Natchpai/Electronic_Load/Electronic_load_esp32/Controller.kicad_sch

## KiCad design Electronic_load_esp32/Controller.kicad_sch (2025-04-01)

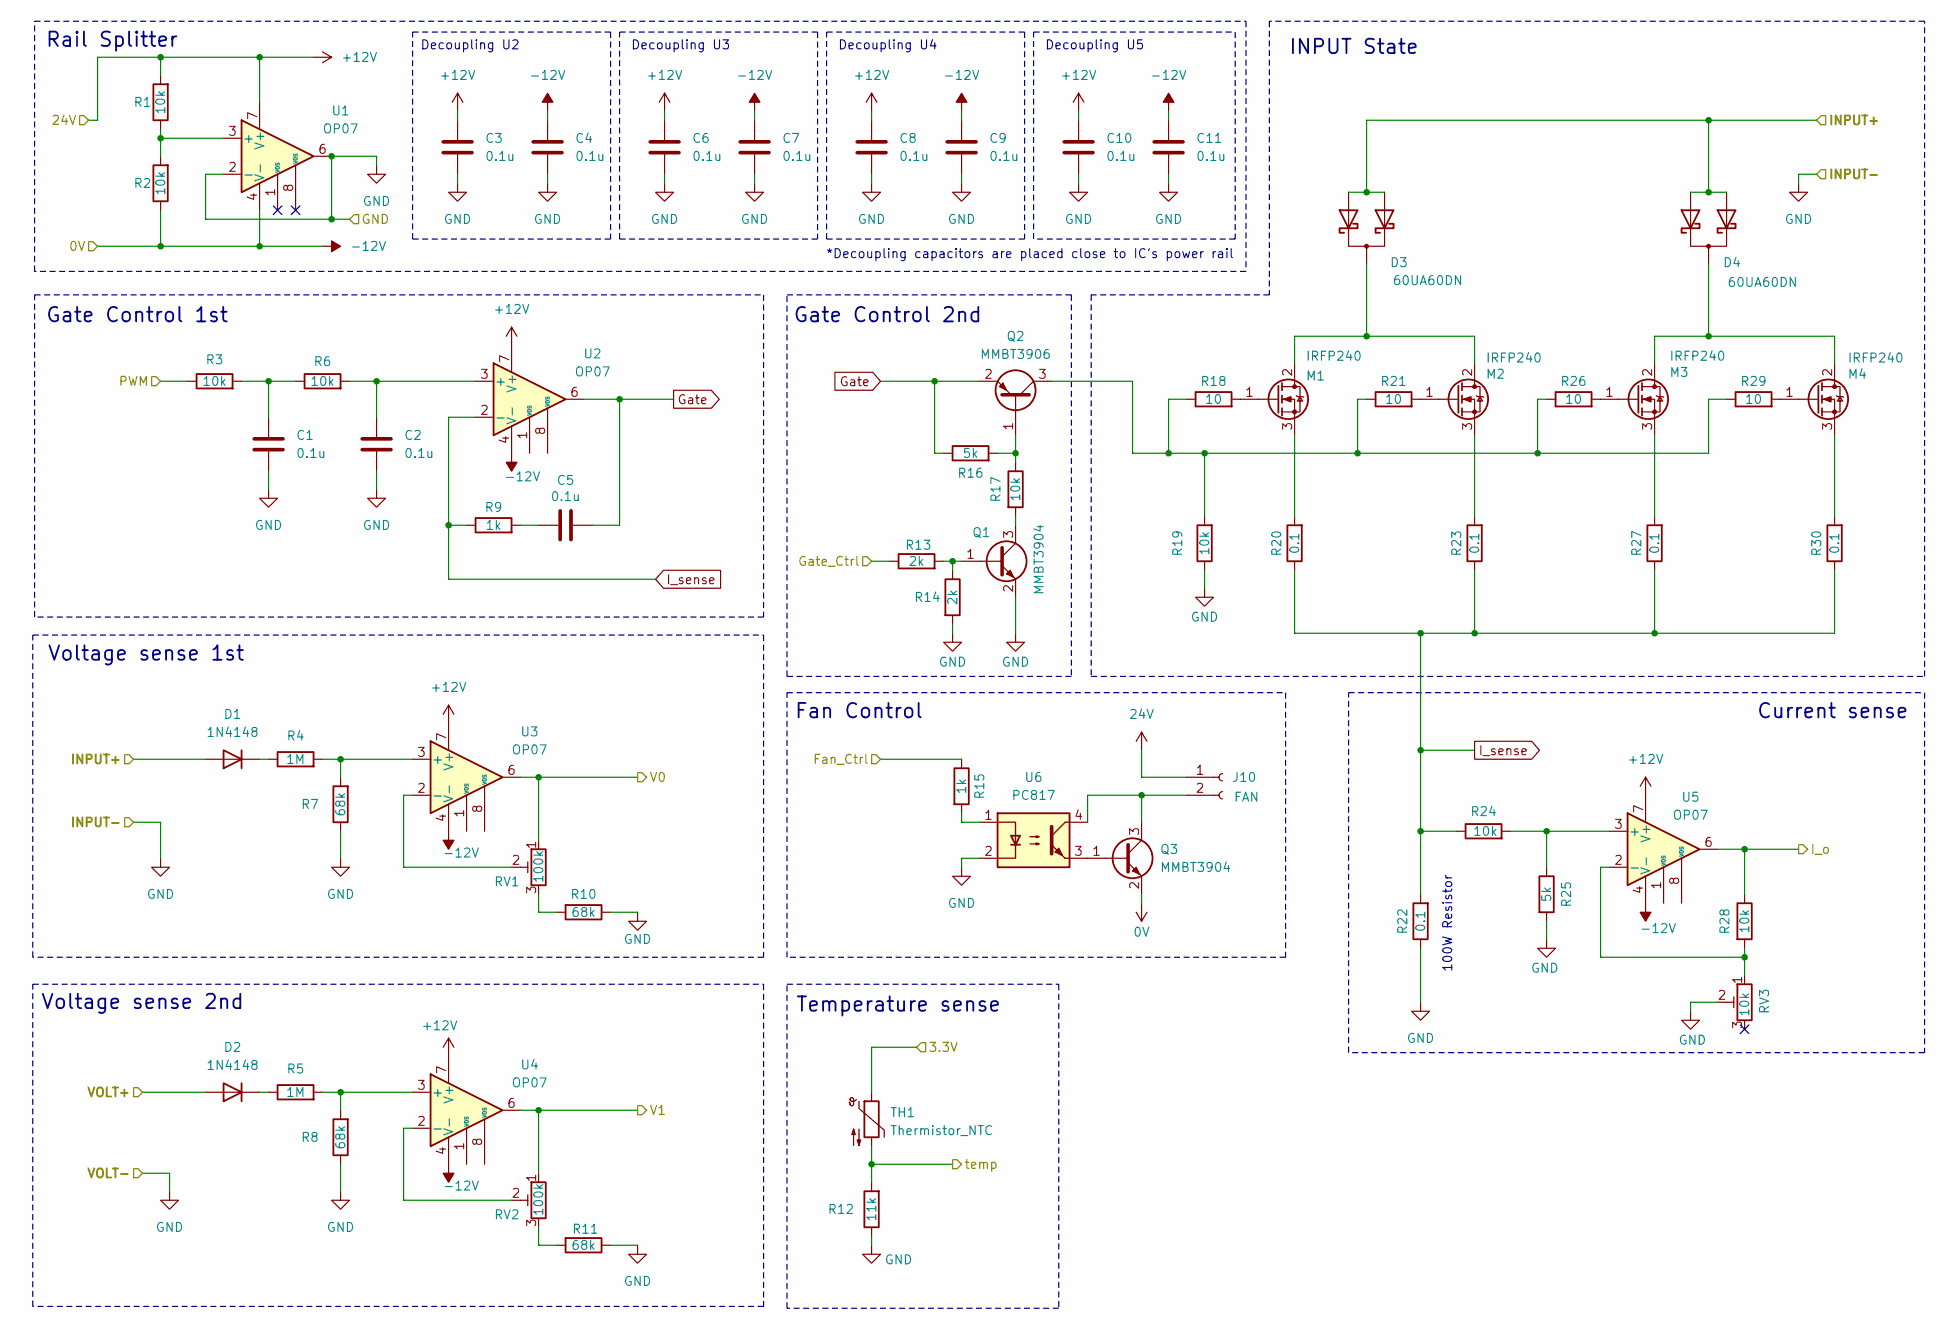
[picture p27: schematic Controller.kicad_sch]

Parts:
C1, C2, C3, C4, C5, C6, C7, C8, C9, C10, C11: 0.1u; C_0603_1608Metric
D1, D2: 1N4148; D_DO-35_SOD27_P7.62mm_Horizontal
D3, D4: 60UA60DN; D_P600_R-6_P12.70mm_Horizontal
J10: FAN; JST_XA_B02B-XASK-1_1x02_P2.50mm_Vertical
M1, M2, M3, M4: IRFP240; TO-247-3_Vertical
Q1, Q3: MMBT3904; SOT-23
Q2: MMBT3906; SOT-23
R1, R2, R3, R6, R17, R19, R24, R28: 10k; R_0603_1608Metric
R4, R5: 1M; R_0603_1608Metric
R7, R8, R10, R11: 68k; R_0603_1608Metric
R9, R15: 1k; R_0603_1608Metric
R12: 11k; R_0603_1608Metric
R13, R14: 2k; R_0603_1608Metric
R16, R25: 5k; R_0603_1608Metric
R18, R21, R26, R29: 10; R_0603_1608Metric
R20, R22, R23, R27, R30: 0.1; R_0603_1608Metric
RV1, RV2: 100k; Potentiometer_Bourns_3386W_Horizontal
RV3: 10k; Potentiometer_Bourns_3386W_Horizontal
TH1: Thermistor_NTC; R_LDR_5.0x4.1mm_P3mm_Vertical
U1, U2, U3, U4, U5: OP07; SOIC-8_3.9x4.9mm_P1.27mm
U6: PC817; DIP-4_W7.62mm_LongPads

Connections:
0V: Q3.2 (E)
3.3V: TH1.1
24V: J10.1
+12V: C3.1, C6.1, C8.1, C10.1, R1.2, U1.7 (V+), U2.7 (V+), U3.7 (V+), U4.7 (V+), U5.7 (V+)
-12V: C4.1, C7.1, C9.1, C11.1, R2.1, U1.4 (V-), U2.4 (V-), U3.4 (V-), U4.4 (V-), U5.4 (V-)
Fan_Ctrl: R15.1
GND: C1.2, C2.2, C3.2, C4.2, C6.2, C7.2, C8.2, C9.2, C10.2, C11.2, Q1.2 (E), R7.1, R8.1, R10.1, R11.1, R12.1, R14.2, R19.1, R22.1, R25.2, RV3.2, U1.2 (-), U1.6, U6.2
Gate: C5.2, Q2.2 (E), R16.1, U2.6
Gate_Ctrl: R13.1
INPUT+: D1.2 (A), D3.1 (A1), D3.3 (A2), D4.1 (A1), D4.3 (A2)
I_o: R28.1, U5.6
I_sense: R9.1, R20.1, R22.2, R23.1, R24.1, R27.1, R30.1, U2.2 (-)
unnamed: C1.1, R3.2, R6.1
unnamed: C2.1, R6.2, U2.3 (+)
unnamed: C5.1, R9.2
unnamed: D1.1 (K), R4.1
unnamed: D2.1 (K), R5.1
unnamed: D3.2 (K), M1.2 (D), M2.2 (D)
unnamed: D4.2 (K), M3.2 (D), M4.2 (D)
unnamed: J10.2, Q3.3 (C), U6.4
unnamed: M1.1 (G), R18.2
unnamed: M1.3 (S), R20.2
unnamed: M2.1 (G), R21.2
unnamed: M2.3 (S), R23.2
unnamed: M3.1 (G), R26.2
unnamed: M3.3 (S), R27.2
unnamed: M4.1 (G), R29.2
unnamed: M4.3 (S), R30.2
unnamed: Q1.1 (B), R13.2, R14.1
unnamed: Q1.3 (C), R17.2
unnamed: Q2.1 (B), R16.2, R17.1
unnamed: Q2.3 (C), R18.1, R19.2, R21.1, R26.1, R29.1
unnamed: Q3.1 (B), U6.3
unnamed: R1.1, R2.2, U1.3 (+)
unnamed: R4.2, R7.2, U3.3 (+)
unnamed: R5.2, R8.2, U4.3 (+)
unnamed: R10.2, RV1.3
unnamed: R11.2, RV2.3
unnamed: R15.2, U6.1
unnamed: R24.2, R25.1, U5.3 (+)
unnamed: R28.2, RV3.1, U5.2 (-)
unnamed: RV1.2, U3.2 (-)
unnamed: RV2.2, U4.2 (-)
PWM: R3.1
V0: RV1.1, U3.6
V1: RV2.1, U4.6
VOLT+: D2.2 (A)
temp: R12.2, TH1.2

Notes on the sheet:
Gate Control 1st
Decoupling U2
Temperature sense
*Decoupling capacitors are placed close to IC's power rail
Current sense
Decoupling U4
Gate Control 2nd
INPUT State
Voltage sense 1st
Decoupling U5
Decoupling U3
Fan Control
100W Resistor
Voltage sense 2nd
Rail Splitter
