Natchpai/Electronic_Load/IMG_8594.JPG

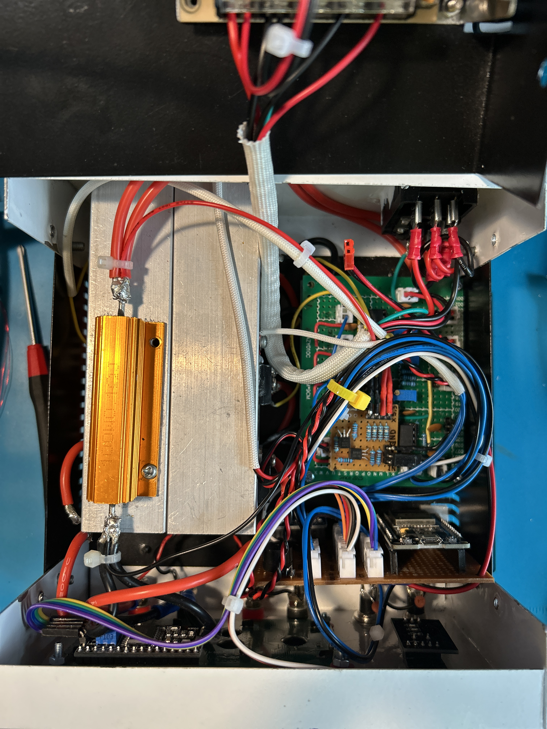
IMG_8594.JPG
